omarcely/AMModulator/Antenna/Sims/AcopleAntena.asc

C1: cap; 33p
C2: cap; 220p
L1: ind; 8.2642µ
L2: ind; {L}; Rser={2*pi*L*28837000/80}
R1: res; 797.3
V1: voltage; ""; AC 1; Rser=50
Named nets: 0
.ac dec 1000 10meg 100meg
.param L = 1.1487u
