omarcely/AMModulator/Mixer/Power Mixer/Mixer.asc

C1: cap; 1n
C2: cap; 100n
C3: cap; 1m
C4: cap; 6.5p
L1: ind; 1m
L2: ind; 4.68µ
Q2: npn; Qmmbt3904lt1g
R1: res; 120
R2: res; 180
R4: res; 27
R5: res; 22k
R6: res; 1.5k
V1: voltage; SINE(0 1 28837500); Rser=50
V2: voltage; 12
V3: voltage; SINE(0 300m 20k); Rser=50
Named nets: 0, V+
.tran 0 300u 100u 0.1n
.MODEL Qmmbt3904lt1g npn
+IS=2.04959e-14 BF=363.202 NF=1.04474 VAF=10
+IKF=0.0238161 ISE=4.06917e-14 NE=1.46344 BR=1.88131
+NR=1.02127 VAR=87.0198 IKR=0.238161 ISC=4.06917e-14
+NC=3.87411 RB=10.62 IRB=24.2417 RBM=10.62
+RE=0.0189075 RC=0.833881 XTB=0.794336 XTI=1
+EG=1.206 CJE=5.01193e-12 VJE=0.4 MJE=0.308747
+TF=4.90228e-10 XTF=9.95281 VTF=0.230247 ITF=0.212393
+CJC=3.75788e-12 VJC=0.4 MJC=0.236094 XCJC=1
+FC=0.8 CJS=0 VJS=0.75 MJS=0.5
+TR=1e-07 PTF=0 KF=0 AF=1
